doesntfazer/MacroMacro/components/Molex/0781271220.stp

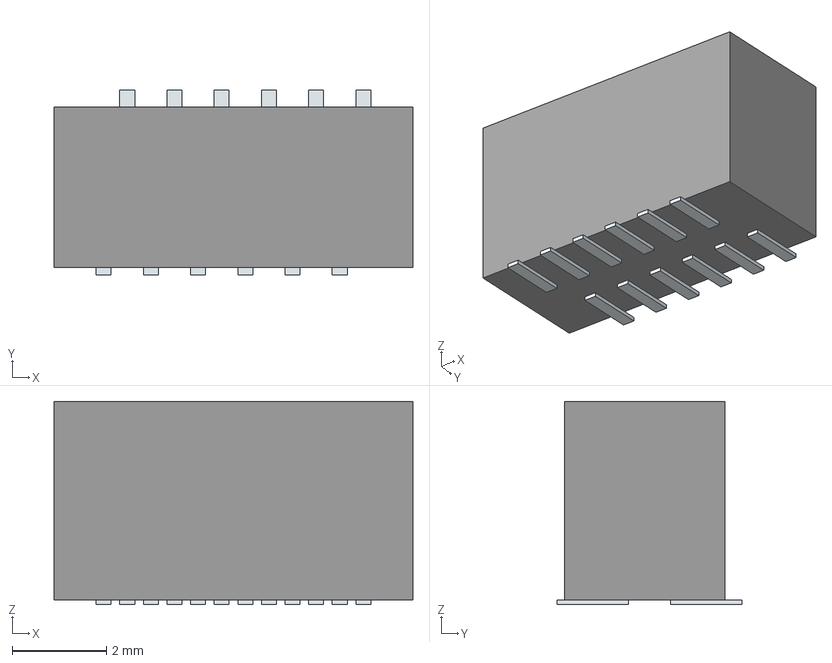
[picture p25: CAD file, 2023-09-12]
components/Molex/0781271220.stp
7.60 x 3.92 x 4.30 mm
Pins
